BrettHallen/Elektronika_MK-66/KiCad/Elektronika_MK-66/Elektronika_MK-66.kicad_pcb

## KiCad design KiCad_Files/ShotClockPCB/ShotClockPCB.kicad_sch

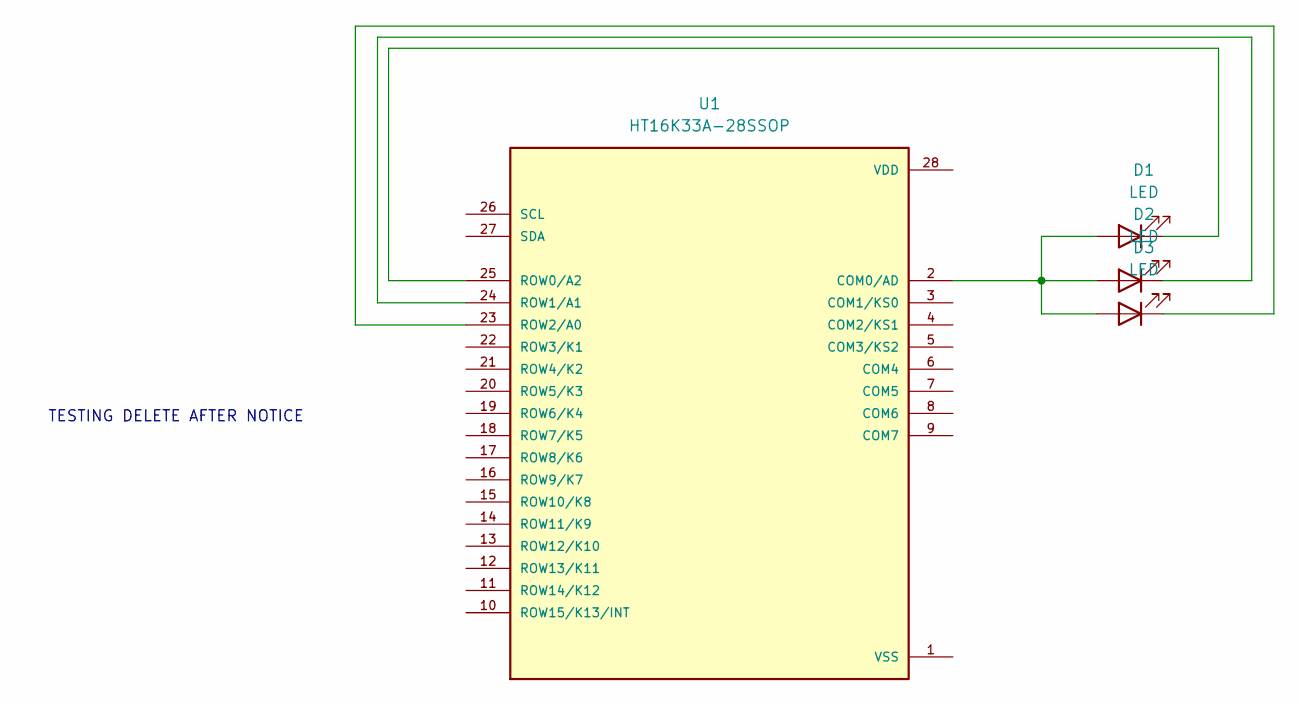
[picture p11: schematic ShotClockPCB.kicad_sch]

Parts:
D1, D2, D3: LED
U1: HT16K33A-28SSOP; SOP63P600X175-28N; PARTREV 1.02

Connections:
unnamed: D1.1 (K), U1.25 (ROW0/A2)
unnamed: D1.2 (A), D2.2 (A), D3.2 (A), U1.2 (COM0/AD)
unnamed: D2.1 (K), U1.24 (ROW1/A1)
unnamed: D3.1 (K), U1.23 (ROW2/A0)

Notes on the sheet:
TESTING DELETE AFTER NOTICE
